Ningel85/ChipELearning/ChipE3D/AttacheP.SLDPRT

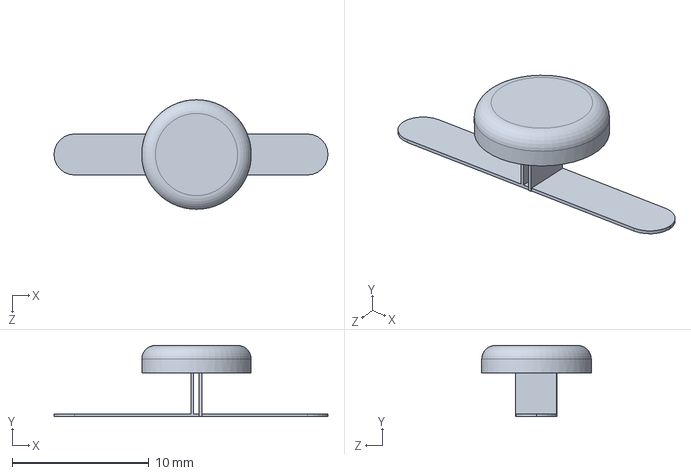
[picture p15: CAD file, 2017-08-02]
ChipE3D/AttacheP.SLDPRT
20.0 x 5.20 x 8.00 mm
