Ningel85/ChipELearning/ChipE3D/LSM303D.SLDPRT

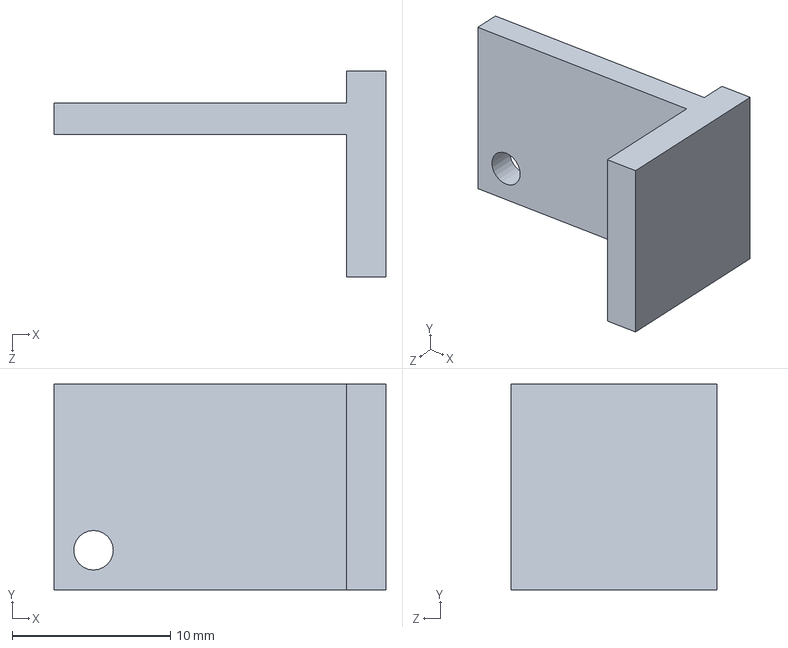
[picture p16: CAD file, 2017-08-02]
ChipE3D/LSM303D.SLDPRT
21.0 x 13.0 x 13.0 mm
