Ningel85/ChipELearning/ChipE3D/Pied.SLDPRT

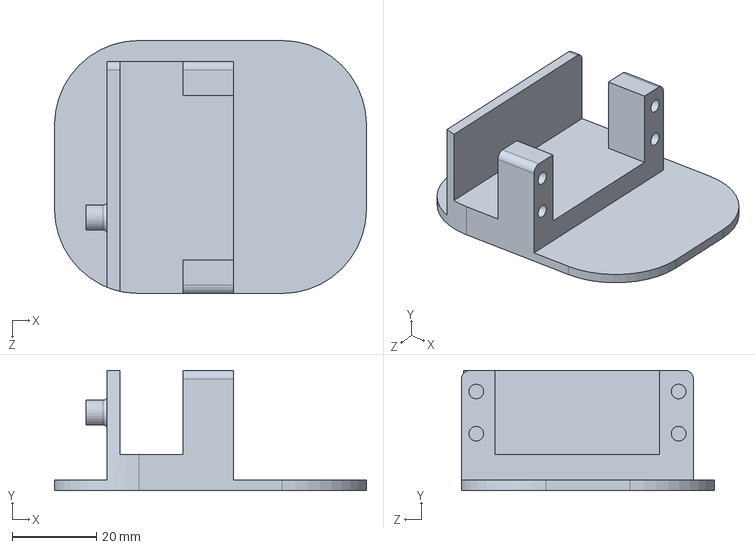
[picture p17: CAD file, 2017-08-02]
ChipE3D/Pied.SLDPRT
74.0 x 28.5 x 60.0 mm
