Ningel85/ChipELearning/ChipE3D/BodyTop.SLDPRT

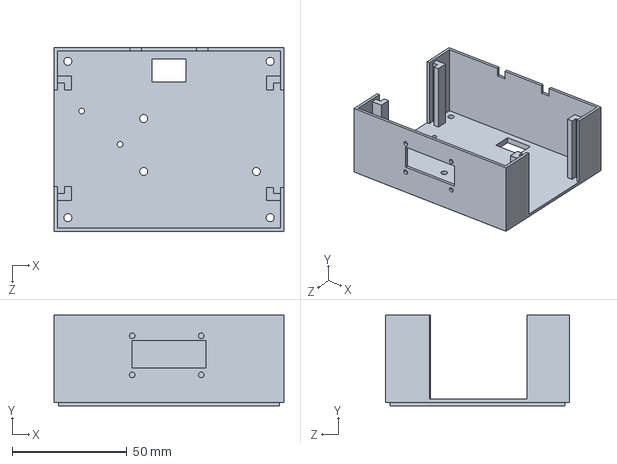
[picture p18: CAD file, 2017-08-02]
ChipE3D/BodyTop.SLDPRT
100.0 x 39.5 x 80.0 mm
