Ningel85/ChipELearning/ChipE3D/Ecran.SLDPRT

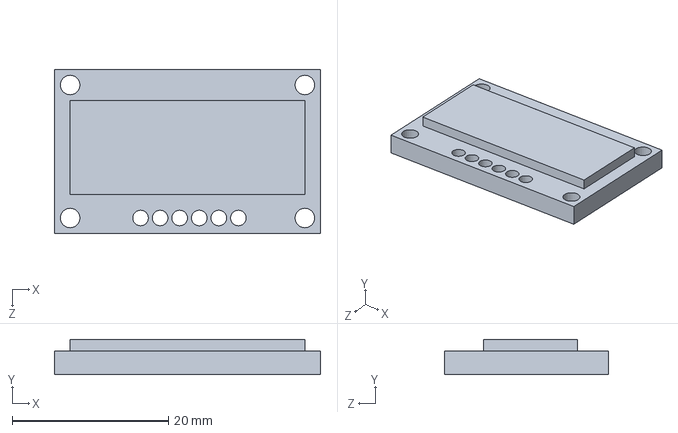
[picture p19: CAD file, 2017-08-02]
ChipE3D/Ecran.SLDPRT
34.0 x 4.50 x 21.0 mm
