Ningel85/ChipELearning/ChipE3D/telecommande.SLDPRT

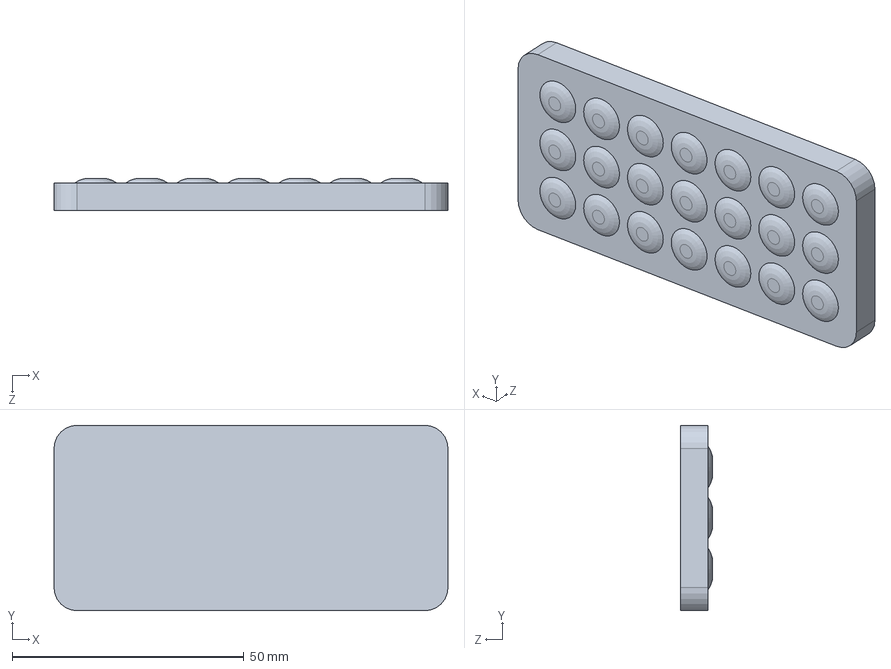
[picture p20: CAD file, 2017-08-02]
ChipE3D/telecommande.SLDPRT
85.0 x 40.0 x 7.00 mm
