Ningel85/ChipELearning/ChipE3D/ServoS1213.SLDPRT

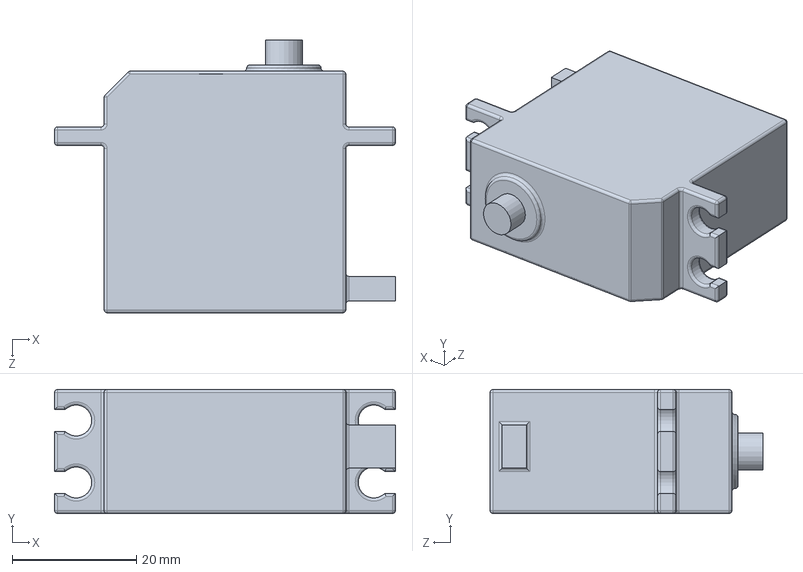
[picture p21: CAD file, 2017-08-02]
ChipE3D/ServoS1213.SLDPRT
55.0 x 20.0 x 44.0 mm
