Ningel85/ChipELearning/ChipE3D/Teensy-bras-corps-base-X4.SLDPRT

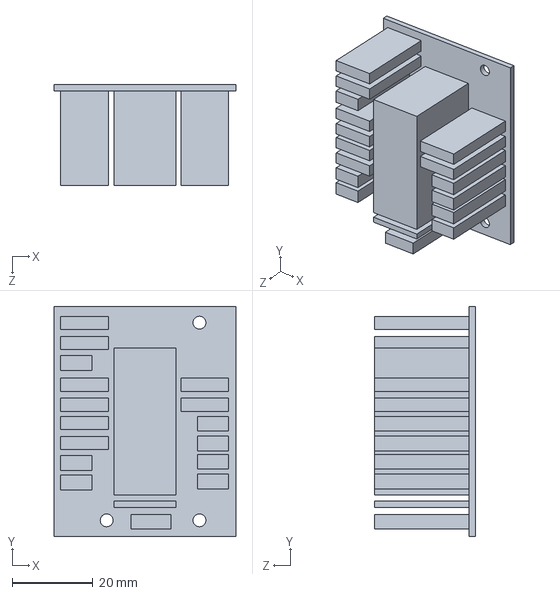
[picture p22: CAD file, 2017-08-02]
ChipE3D/Teensy-bras-corps-base-X4.SLDPRT
45.0 x 57.0 x 25.0 mm
