Ningel85/ChipELearning/ChipE3D/epaule.SLDPRT

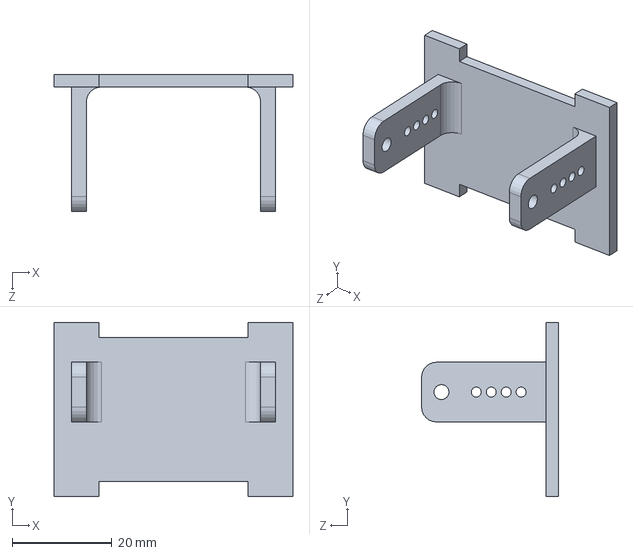
[picture p23: CAD file, 2017-08-02]
ChipE3D/epaule.SLDPRT
48.0 x 35.0 x 27.5 mm
